cristianoag/esp32_clones/hardware/cases/apple2/preview.png

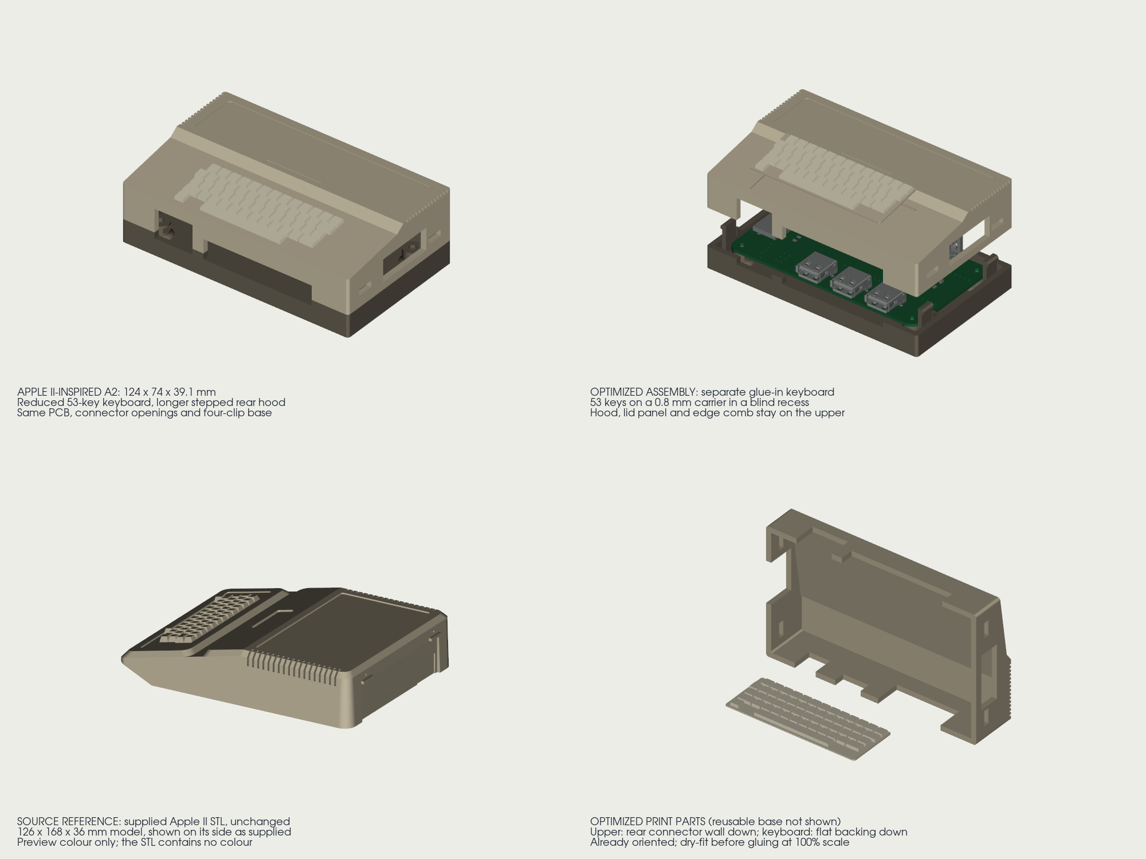
hardware/cases/apple2/preview.png
