cristianoag/esp32_clones/hardware/cases/hb-8000/preview.png

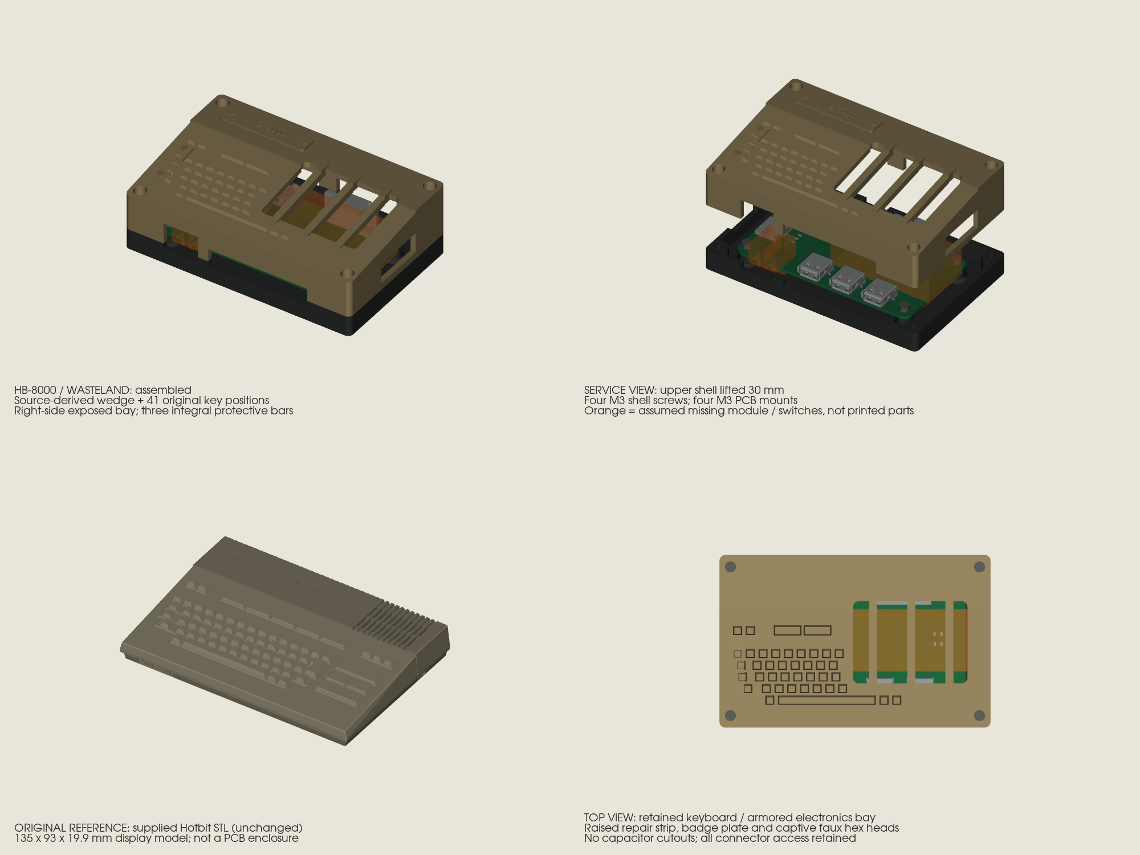
hardware/cases/hb-8000/preview.png
