cristianoag/esp32_clones/images/board-back.png

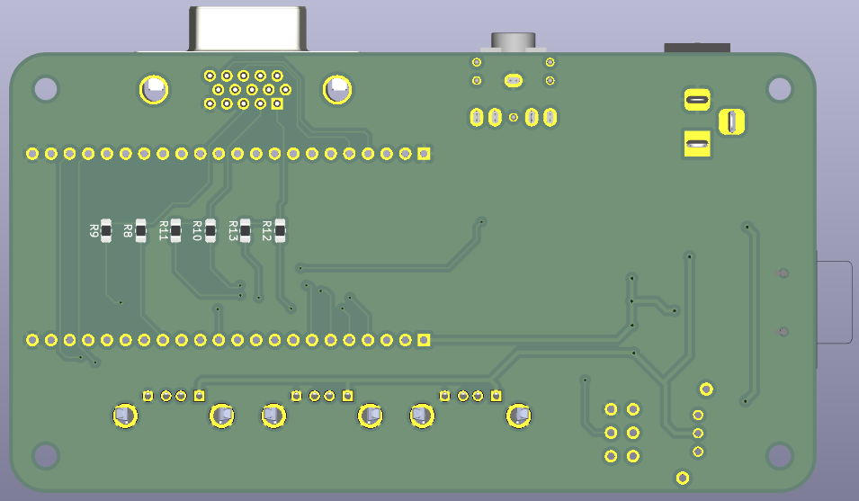
images/board-back.png
