cristianoag/esp32_clones/images/board-front.png

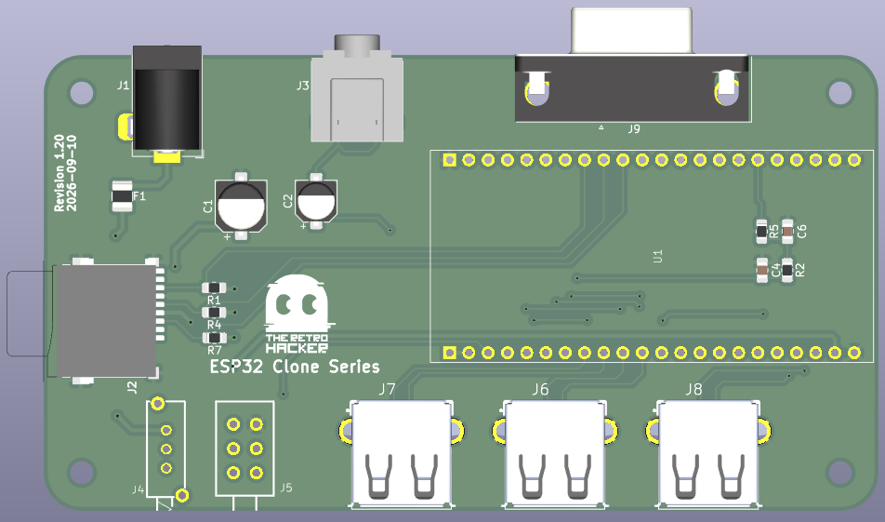
images/board-front.png
