cristianoag/esp32_clones/images/prologica.png

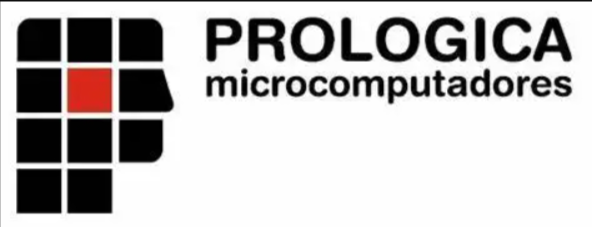
images/prologica.png
