cristianoag/esp32_clones/hardware/cases/caps/PS-12E05_cap.stl

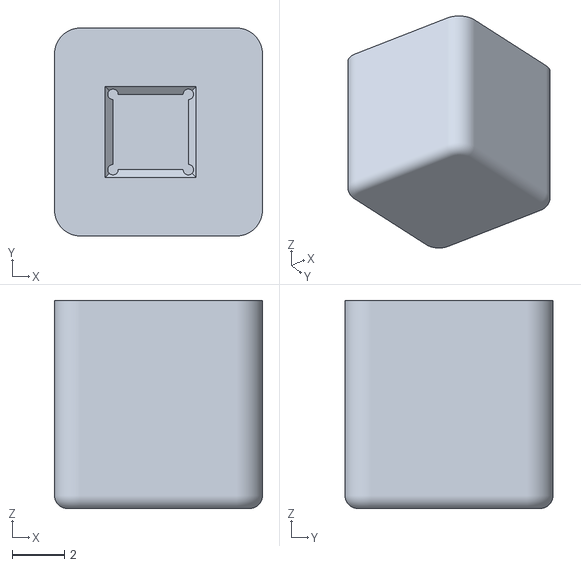
[picture p27: CAD file, 2026-10-05]
hardware/cases/caps/PS-12E05_cap.stl
8.00 x 8.00 x 8.00
