cristianoag/esp32_clones/hardware/cases/sony/f1xd_keyboard_optimized.stl

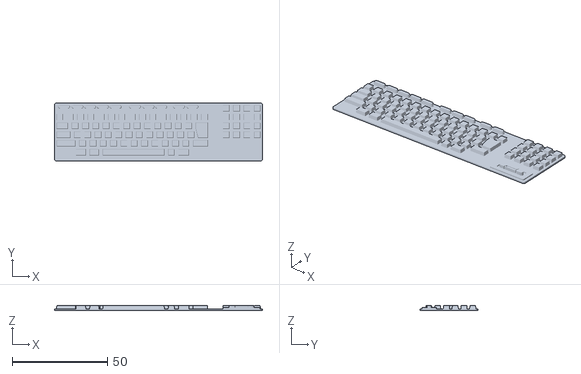
[picture p28: CAD file, 2026-10-08]
hardware/cases/sony/f1xd_keyboard_optimized.stl
109.3 x 30.4 x 2.45
