cristianoag/esp32_clones/hardware/cases/standard/upper_shell_vented.stl

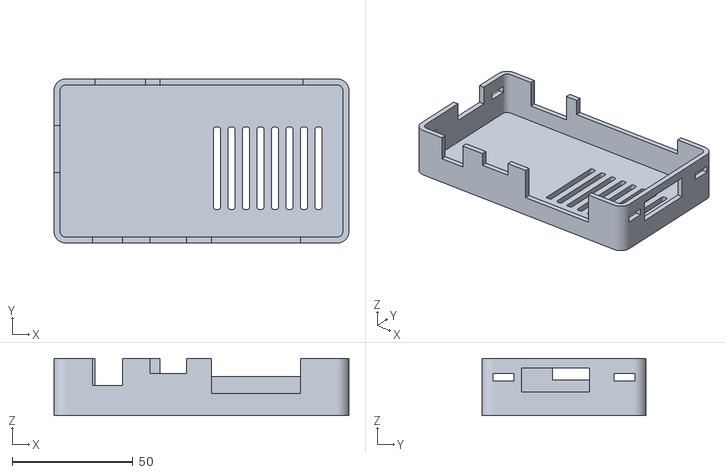
[picture p29: CAD file, 2026-10-03]
hardware/cases/standard/upper_shell_vented.stl
122.0 x 68.0 x 23.7
