cristianoag/esp32_clones/hardware/cases/apple2/apple2_base.stl

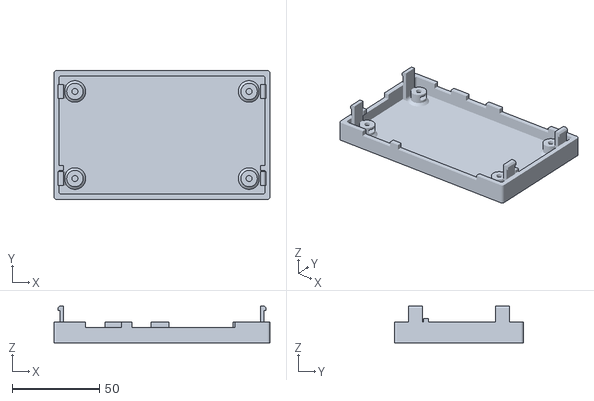
[picture p30: CAD file, 2026-10-06]
hardware/cases/apple2/apple2_base.stl
124.0 x 74.0 x 21.2
