cristianoag/esp32_clones/hardware/cases/hb-8000/wasteland_upper.stl

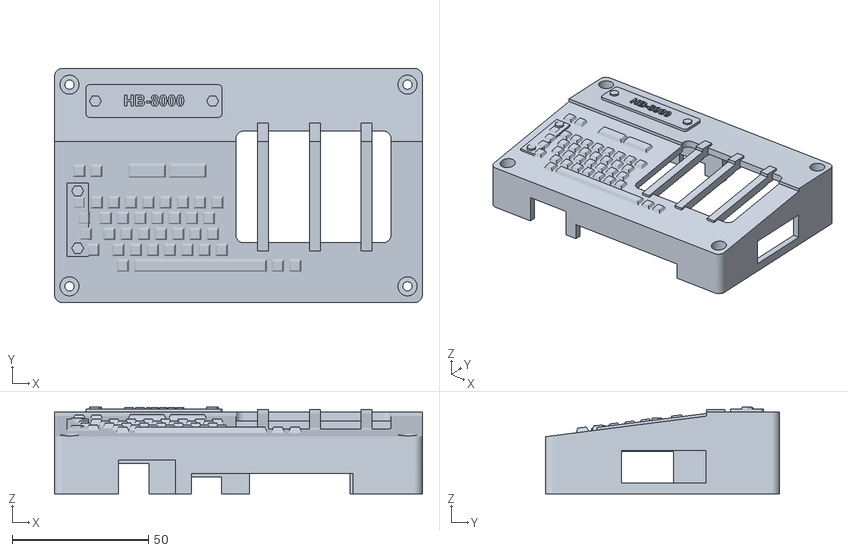
[picture p31: CAD file, 2026-10-03]
hardware/cases/hb-8000/wasteland_upper.stl
135.0 x 86.0 x 31.9
