cristianoag/esp32_clones/hardware/cases/sony/f1xd_drive_red.stl

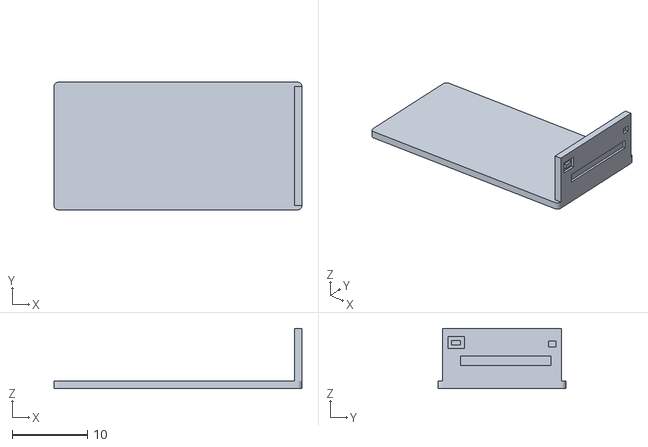
[picture p32: CAD file, 2026-10-08]
hardware/cases/sony/f1xd_drive_red.stl
33.0 x 17.0 x 8.00
