cristianoag/esp32_clones/hardware/cases/standard/lid.stl

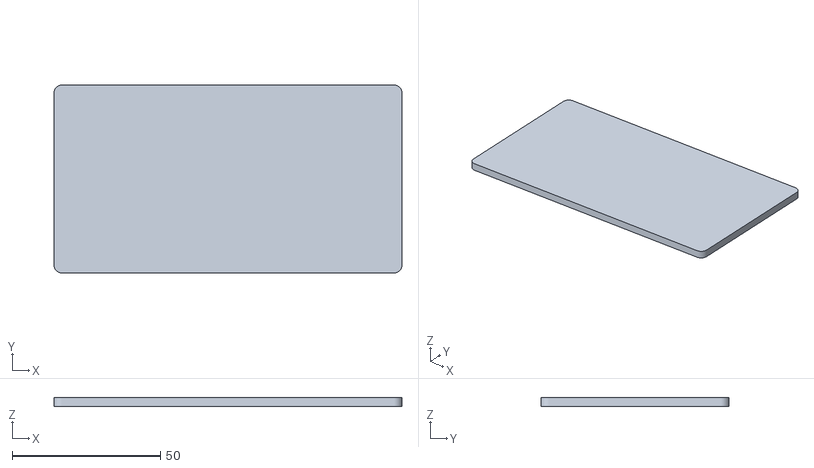
[picture p33: CAD file, 2026-10-03]
hardware/cases/standard/lid.stl
117.4 x 63.4 x 3.00
