cristianoag/esp32_clones/hardware/cases/apple2/APPLE2_1_3_scale.stl

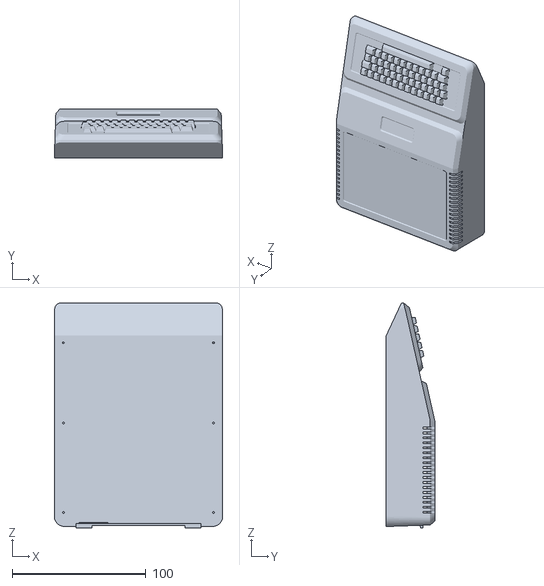
[picture p34: CAD file, 2026-10-03]
hardware/cases/apple2/APPLE2_1_3_scale.stl
126.1 x 36.3 x 168.4
