cristianoag/esp32_clones/hardware/cases/hb-8000/HB-8000_1_3_scale_open.stl

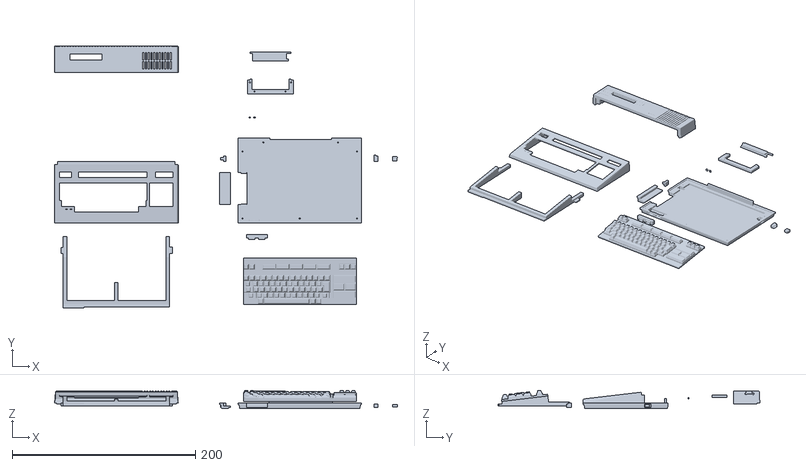
[picture p35: CAD file, 2026-10-03]
hardware/cases/hb-8000/HB-8000_1_3_scale_open.stl
374.1 x 285.5 x 19.9
