cristianoag/esp32_clones/hardware/cases/panasonic/a1st_keyboard_optimized.stl

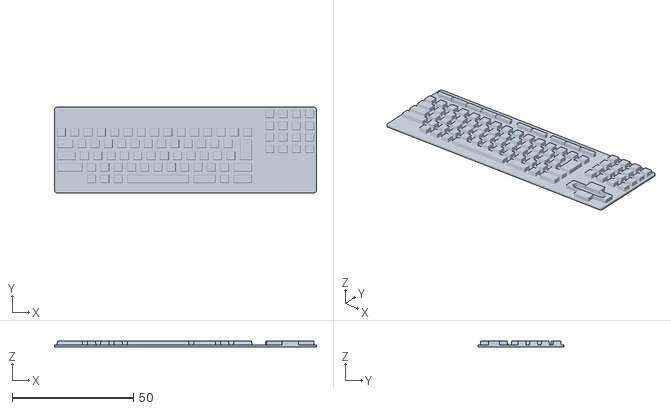
[picture p36: CAD file, 2026-10-08]
hardware/cases/panasonic/a1st_keyboard_optimized.stl
108.0 x 35.3 x 2.45
