cristianoag/esp32_clones/hardware/cases/sony/HB-F1XD_1_3_scale.stl

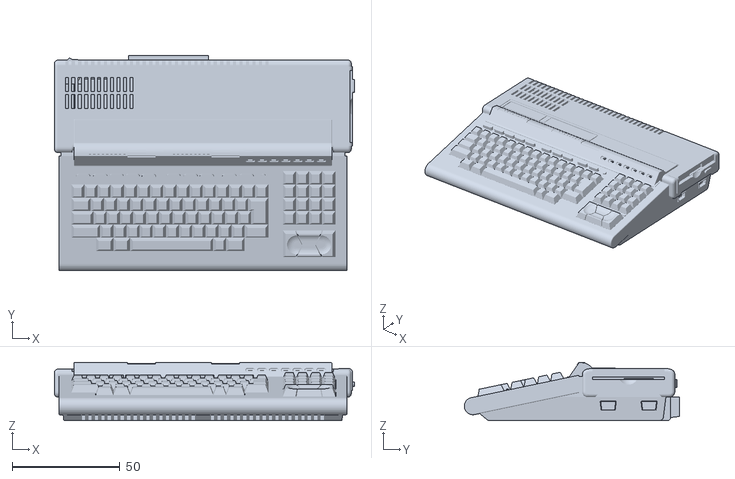
[picture p37: CAD file, 2026-10-08]
hardware/cases/sony/HB-F1XD_1_3_scale.stl
139.5 x 100.2 x 27.2
