cristianoag/esp32_clones/hardware/cases/apple2/APPLE2_1_3_scale_open.stl

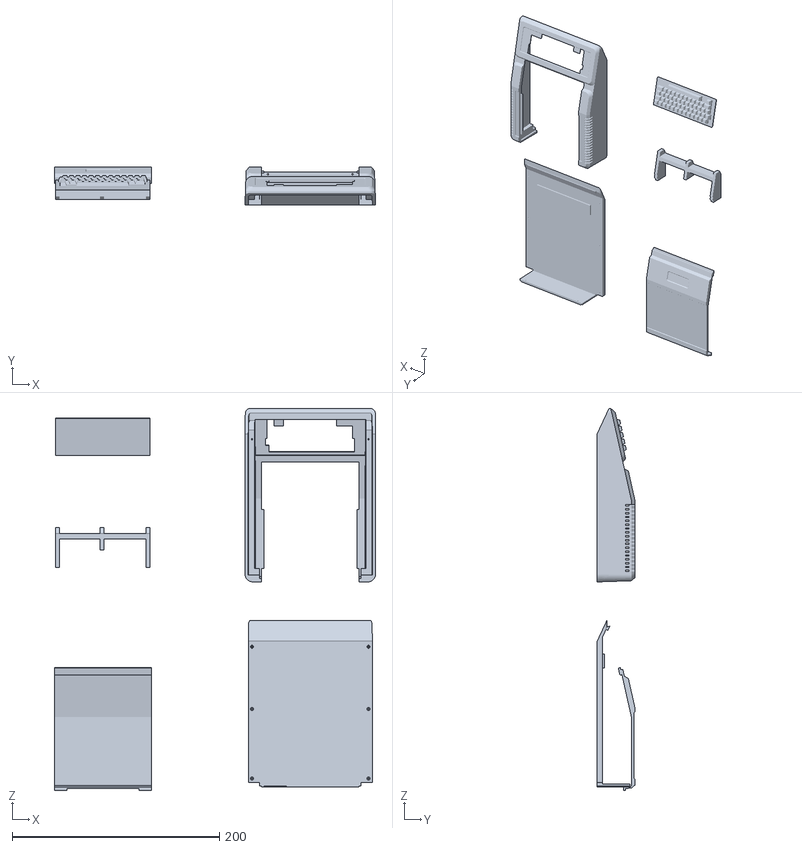
[picture p38: CAD file, 2026-10-03]
hardware/cases/apple2/APPLE2_1_3_scale_open.stl
309.9 x 36.3 x 368.4
