cristianoag/esp32_clones/hardware/cases/hb-8000/wasteland_base.stl

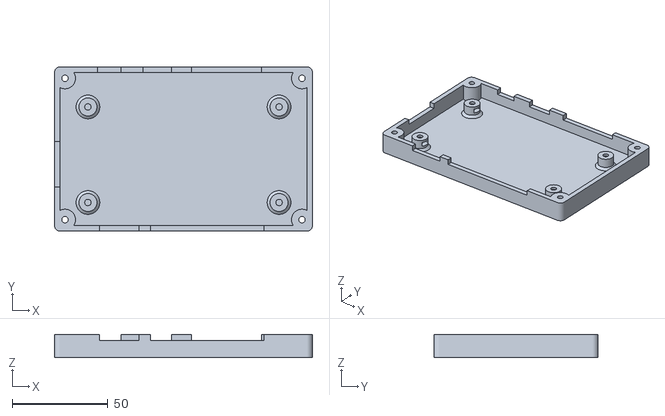
[picture p39: CAD file, 2026-10-03]
hardware/cases/hb-8000/wasteland_base.stl
135.0 x 86.0 x 12.1
