cristianoag/esp32_clones/hardware/cases/sony/HB-F1XD_1_3_scale_open.stl

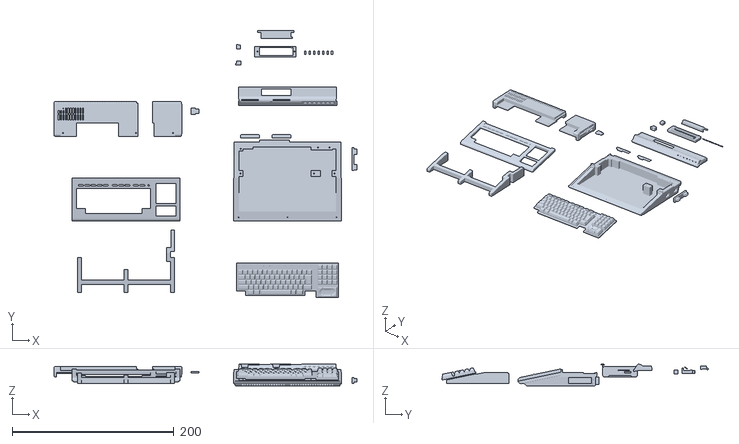
[picture p40: CAD file, 2026-10-08]
hardware/cases/sony/HB-F1XD_1_3_scale_open.stl
374.9 x 330.0 x 27.2
