cristianoag/esp32_clones/hardware/cases/apple2/APPLE2_1_3_scale_open2.stl

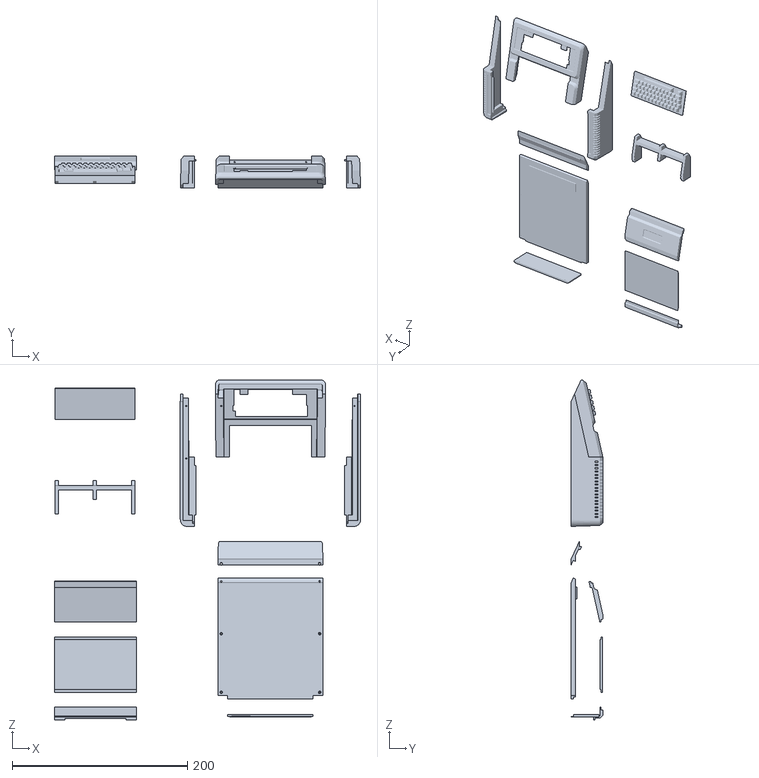
[picture p41: CAD file, 2026-10-03]
hardware/cases/apple2/APPLE2_1_3_scale_open2.stl
349.9 x 36.3 x 388.4
