cristianoag/esp32_clones/hardware/cases/hb-8000/HB-8000_1_3_scale.stl

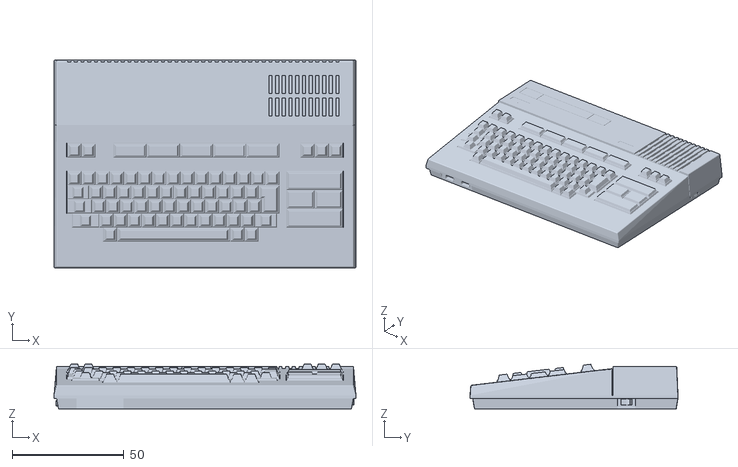
[picture p42: CAD file, 2026-10-03]
hardware/cases/hb-8000/HB-8000_1_3_scale.stl
135.0 x 93.0 x 19.9
