cristianoag/esp32_clones/software/esp32_cp400_emulator/src/CP400Roms.h

/******************************************************************************
 * Project      : esp32_cp400_emulator
 * File         : CP400Roms.h
 * Last Updated : 2026-08-17
 *
 * Description  : Font images used to emulate the CP400 video output
 *
 * Original work copyright (c) 2026 Cedric Beaudoin
 * CP400 code and modifications copyright (c) 2026 The Retro Hacker
 *
 * Permission is granted for personal, non-commercial use only.
 * Commercial use, distribution, sublicensing, or modification
 * for commercial purposes is strictly prohibited without
 * prior written permission from the author.
 * Please, keep this in the source code.
 * All rights reserved.
 ******************************************************************************/

#ifndef CP400_ROMS_H
#define CP400_ROMS_H

#include <stdint.h>


const uint8_t font_gimeChip[1536] = {
	0x00, 0x38, 0x44, 0x40, 0x40, 0x40, 0x44, 0x38, 0x10, 0x00, 0x00, 0x00,
	0x00, 0x44, 0x00, 0x44, 0x44, 0x44, 0x4c, 0x34, 0x00, 0x00, 0x00, 0x00,
	0x00, 0x08, 0x10, 0x38, 0x44, 0x7c, 0x40, 0x38, 0x00, 0x00, 0x00, 0x00,
	0x00, 0x10, 0x28, 0x38, 0x04, 0x3c, 0x44, 0x3c, 0x00, 0x00, 0x00, 0x00,
	0x00, 0x28, 0x00, 0x38, 0x04, 0x3c, 0x44, 0x3c, 0x00, 0x00, 0x00, 0x00,
	0x00, 0x20, 0x10, 0x38, 0x04, 0x3c, 0x44, 0x3c, 0x00, 0x00, 0x00, 0x00,
	0x00, 0x10, 0x00, 0x38, 0x04, 0x3c, 0x44, 0x3c, 0x00, 0x00, 0x00, 0x00,
	0x00, 0x00, 0x00, 0x38, 0x44, 0x40, 0x44, 0x38, 0x10, 0x00, 0x00, 0x00,
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
	0xff, 0xff, 0xff, 0xff, 0xff, 0xff, 0x0f, 0x0f, 0x0f, 0x0f, 0x0f, 0x0f, //13
	0xff, 0xff, 0xff, 0xff, 0xff, 0xff, 0xf0, 0xf0, 0xf0, 0xf0, 0xf0, 0xf0, //14
	0xff, 0xff, 0xff, 0xff, 0xff, 0xff, 0xff, 0xff, 0xff, 0xff, 0xff, 0xff, //15

};









#endif
