cristianoag/esp32_clones/software/esp32_msx_emulator/src/MsxCore.cpp

#include "MsxCore.h"
#include "MsxPlatform.h"
#include "Esp32Port.h"
#include "FramePacer.h"
#include "WorkProfile.h"
#include "MSX.h"
#include "Sound.h"
#include "MapperDatabase.h"
#include "AudioProfiles.h"
#include <esp_heap_caps.h>
#include <stdio.h>
#include <string.h>
#include <errno.h>
#include <sys/stat.h>
#ifdef ESP_PLATFORM
#include <esp_timer.h>
#include <freertos/FreeRTOS.h>
#include <freertos/task.h>
#endif

// Common.h needs side borders for the VDP horizontal-adjust register.
#define WIDTH 272
#define HEIGHT 240
static_assert(sizeof(pixel) == 1, "fMSX requires BPP8");
static pixel* XBuf;
static unsigned int XPal[80], BPal[256], XPal0;
static uint32_t rgbPalette[256];
static char biosDirectory[256];
static unsigned audioFraction;
static bool running;
static bool allocationFailed;
#ifdef ESP_PLATFORM
static FramePacer framePacer;
static int64_t lastYield, speedStart;
static unsigned speedFrames, speedPresented;
static FmsxWorkProfile workProfile;
extern "C" {
unsigned char fmsxProfileActive=0;
void fmsxProfileBegin(unsigned section) { workProfile.begin(section,esp_timer_get_time()); }
void fmsxProfileEnd(unsigned section) { workProfile.end(section,esp_timer_get_time()); }
}
#endif
static void PutImage();
#include "Common.h"

extern "C" void* fmsxAllocate(size_t size)
{
  void* p = heap_caps_malloc(size, MALLOC_CAP_SPIRAM | MALLOC_CAP_8BIT);
  if (!p) { allocationFailed = true; errno = ENOMEM; }
  return p;
}

extern "C" void* fmsxAllocateCpu(size_t size)
{
#ifdef ESP_PLATFORM
  // Keep video/large mapper buffers in PSRAM and leave headroom for other tasks.
  constexpr size_t reserve = 64U * 1024U;
  constexpr unsigned caps = MALLOC_CAP_INTERNAL | MALLOC_CAP_8BIT;
  void* p = nullptr;
  if (size <= 64U * 1024U && heap_caps_get_free_size(caps) >= size + reserve)
    p = heap_caps_malloc(size, caps);
  if (p) {
    printf("MSX CPU memory: %u bytes in internal SRAM\n", static_cast<unsigned>(size));
    return p;
  }
  printf("MSX CPU memory: %u bytes in PSRAM (size/reserve/fragmentation fallback)\n",
         static_cast<unsigned>(size));
#endif
  return fmsxAllocate(size);
}

extern "C" FILE* fmsxOpen(const char* name, const char* mode)
{
  if (!name) { errno = EINVAL; return nullptr; }
  if (name[0] == '/') return fopen(name, mode);
  char path[512];
  const int n = snprintf(path, sizeof(path), "%s/%s", biosDirectory, name);
  if (n < 0 || n >= static_cast<int>(sizeof(path))) {
    errno = ENAMETOOLONG;
    return nullptr;
  }
  return fopen(path, mode);
}

extern "C" void fmsxMediaYield()
{
#ifdef ESP_PLATFORM
  vTaskDelay(1);
#endif
}

extern "C" void fmsxFrame()
{
#ifdef ESP_PLATFORM
  int64_t now = esp_timer_get_time();
  workProfile.finishFrame(now);
  fmsxProfileActive=0;
  const int64_t wait = framePacer.frame(now, PALVideo);
  const int64_t target = now + wait;
  while (now < target) {
    TickType_t ticks = pdMS_TO_TICKS((target - now) / 1000);
    vTaskDelay(ticks ? ticks : 1);
    now = esp_timer_get_time();
    lastYield = now;
  }
  // Yield periodically when behind, not on every frame (one tick can be costly).
  if (now - lastYield >= 50000) {
    vTaskDelay(1);
    now = esp_timer_get_time();
    lastYield = now;
  }
  UPeriod = framePacer.renderingPercent();
  if (!speedStart) {
    speedStart = now;
    speedFrames = speedPresented = 0;
  } else ++speedFrames;
  const int64_t elapsed = now - speedStart;
  if (elapsed >= 5000000) {
    printf("MSX speed: %.1f/%u emulated fps, %.1f presented fps, draw=%u%%\n",
           speedFrames * 1000000.0 / elapsed, PALVideo ? 50U : 60U,
           speedPresented * 1000000.0 / elapsed, static_cast<unsigned>(UPeriod));
    if(workProfile.samples)
    {
      const double scale=1.0/(1000.0*workProfile.samples);
      printf("MSX work: samples=%u total=%.2f cpu/other=%.2f vdp=%.2f draw=%.2f blit=%.2f sprites=%.2f audio=%.2f input=%.2f ms/frame\n",
             workProfile.samples,workProfile.total*scale,workProfile.cpuOther()*scale,
             workProfile.times[FmsxWorkVdp]*scale,workProfile.times[FmsxWorkDraw]*scale,
             workProfile.times[FmsxWorkBlit]*scale,workProfile.times[FmsxWorkSprites]*scale,
             workProfile.times[FmsxWorkAudio]*scale,workProfile.times[FmsxWorkInput]*scale);
    }
    workProfile.clearWindow();
    speedStart = now;
    speedFrames = speedPresented = 0;
  }
  now=esp_timer_get_time();
  framePacer.released(now);
  fmsxProfileActive=workProfile.startFrame(now);
#endif
  if (msxShouldExit()) ExitNow = 1;
}

static void PutImage()
{
  FMSX_WORK_BEGIN(FmsxWorkBlit);
  const int width = 256;
  msxPresent(XBuf + (WIDTH - width) / 2, width, HEIGHT, rgbPalette, WIDTH);
  FMSX_WORK_END(FmsxWorkBlit);
#ifdef ESP_PLATFORM
  ++speedPresented;
#endif
  if (msxShouldExit()) ExitNow = 1;
}

extern "C" void SetColor(byte n, byte r, byte g, byte b)
{
  if (n >= 80) return;
  // A fixed GGGRRRBB palette preserves scanline palette changes and SCREEN 8/YJK.
  XPal[n] = (g & 0xE0) | ((r & 0xE0) >> 3) | (b >> 6);
  if (!n) XPal0 = XPal[n];
}

extern "C" void Keyboard()
{
  uint8_t matrix[16];
  memset(matrix, 0xFF, sizeof(matrix));
#ifdef ESP_PLATFORM
  const int64_t pollStart = esp_timer_get_time();
#endif
  msxPollKeyboard(matrix);
#ifdef ESP_PLATFORM
  // F12 menus block inside the platform callback. Discard their wall time/debt.
  if (esp_timer_get_time() - pollStart >= 100000) {
    framePacer.reset(true);
    workProfile.reset();
    fmsxProfileActive=0;
    speedStart = 0;
    speedFrames = speedPresented = 0;
  }
#endif
  for (unsigned i = 0; i < sizeof(matrix); ++i) KeyState[i] = matrix[i];
  if (msxShouldExit()) ExitNow = 1;
}

extern "C" unsigned int Joystick() { return msxPollJoysticks() & 0x3f3f; }
extern "C" unsigned int Mouse(byte) { return 0; }
extern "C" unsigned int InitAudio(unsigned int rate, unsigned int) { return rate; }
extern "C" void TrashAudio() {}
extern "C" unsigned int GetFreeAudio() { return 1024; }
extern "C" unsigned int WriteAudio(sample* data, unsigned int count)
{
  static_assert(sizeof(sample) == sizeof(int16_t), "fMSX requires BPS16");
  msxSubmitAudio(data, count);
  return count;
}

extern "C" void PlayAllSound(int microseconds)
{
  audioFraction += static_cast<unsigned>(microseconds) * 22050U;
  const unsigned samples = audioFraction / 1000000U;
  audioFraction %= 1000000U;
  if (samples) RenderAndPlayAudio(samples);
}

bool MsxValidateCartridge(const char* path, char* error, size_t errorSize)
{
  if (error && errorSize) error[0] = 0;
  if (!path || !*path) return true;
  const char* problem = nullptr;
  struct stat info;
  if (path[0] != '/')
    problem = "requires an absolute path";
  else if (stat(path, &info) != 0 || !S_ISREG(info.st_mode))
    problem = "file is missing or is not a regular file";
  else if (info.st_size < 8192 || info.st_size > MSX_MAX_CART_BYTES ||
           (info.st_size % 8192) != 0)
    problem = "invalid ROM size (8 KiB multiples, maximum 2 MiB)";
  if (!problem) {
    FILE* file = fopen(path, "rb");
    if (!file) problem = "cannot open cartridge ROM";
    else {
      bool signature = false;
      const long offsets[] = {0, 0x4000, static_cast<long>(info.st_size) - 0x4000};
      for (long offset : offsets) {
        if (offset < 0 || offset + 2 > info.st_size) continue;
        unsigned char header[2];
        if (fseek(file, offset, SEEK_SET) != 0 ||
            fread(header, 1, sizeof(header), file) != sizeof(header)) {
          problem = "cannot read cartridge ROM header";
          break;
        }
#ifdef ESP_PLATFORM
        vTaskDelay(1);
#endif
        if (header[0] == 'A' && header[1] == 'B') { signature = true; break; }
      }
      if (!problem && !signature) problem = "invalid cartridge ROM (AB header not found)";
      fclose(file);
    }
  }
  if (problem && error && errorSize) snprintf(error, errorSize, "%s", problem);
  return !problem;
}

static bool validateCartridge(const char* path, int slot)
{
  char error[128];
  if (MsxValidateCartridge(path, error, sizeof(error))) return true;
  char message[192];
  snprintf(message, sizeof(message), "MSX slot %d: %s.", slot, error);
  msxReportError(message);
  return false;
}

static bool mediaResult(const char* problem, char* error, size_t size)
{
  if (error && size) snprintf(error, size, "%s", problem ? problem : "");
  return !problem;
}

bool MsxInspectCartridge(const char* path, const char* profileDirectory,
                         MsxCartridgeInfo& info, char* error, size_t errorSize)
{
  if (!path || !*path || !profileDirectory || profileDirectory[0] != '/' ||
      strlen(profileDirectory) >= sizeof(biosDirectory))
    return mediaResult("inspection requires cartridge and absolute BIOS directory", error, errorSize);
  if (!MsxValidateCartridge(path, error, errorSize)) return false;
  struct stat fileInfo;
  if (stat(path, &fileInfo) || fileInfo.st_size < 8192 ||
      fileInfo.st_size > MSX_MAX_CART_BYTES || fileInfo.st_size % 8192)
    return mediaResult("cartridge size changed during inspection", error, errorSize);
  FILE* file = fopen(path, "rb");
  if (!file) return mediaResult("cannot open cartridge for inspection", error, errorSize);
  const size_t size = static_cast<size_t>(fileInfo.st_size);
  auto* data = static_cast<unsigned char*>(heap_caps_malloc(size, MALLOC_CAP_SPIRAM | MALLOC_CAP_8BIT));
  if (!data) {
    fclose(file);
    return mediaResult("not enough PSRAM to inspect cartridge; previous selection retained", error, errorSize);
  }
  const char* problem = nullptr;
  for (size_t offset = 0; offset < size;) {
    const size_t count = size - offset < 16384 ? size - offset : 16384;
    if (fread(data + offset, 1, count, file) != count) { problem = "cannot fully read cartridge"; break; }
    offset += count;
#ifdef ESP_PLATFORM
    vTaskDelay(1);
#endif
  }
  if (!problem && (fgetc(file) != EOF || ferror(file))) problem = "cartridge changed during inspection";
  fclose(file);
  FILE* databases[2] = {};
  MsxCartridgeInfo detected = {-1, "ROM layout"};
  if (!problem) {
    const bool ab0 = data[0] == 'A' && data[1] == 'B';
    const bool ab4000 = size > 0x4001 && data[0x4000] == 'A' && data[0x4001] == 'B';
    const bool abLast = size >= 16384 && data[size - 16384] == 'A' && data[size - 16383] == 'B';
    if (!ab0 && !ab4000 && !abLast) problem = "cartridge header changed during inspection";
    else if (size > 32768 && !(!ab0 && ab4000)) {
      const char* names[] = {"CARTS.CRC", "CARTS.SHA"};
      for (unsigned i = 0; i < 2; ++i) {
        char databasePath[512];
        snprintf(databasePath, sizeof(databasePath), "%s/%s", profileDirectory, names[i]);
        errno = 0;
        databases[i] = fopen(databasePath, "rb");
        if (!databases[i] && errno != ENOENT) { problem = "cannot read mapper override database"; break; }
      }
      if (!problem) {
        detected.detectedMapper = GuessROMWithFiles(data, size, databases[0], databases[1], &detected.source);
        if (detected.detectedMapper <= -100) problem = FmsxUnsupportedMapperName(detected.detectedMapper);
      }
    }
  }
  for (FILE* database : databases) if (database) fclose(database);
  heap_caps_free(data);
  if (!problem) info = detected;
  return mediaResult(problem, error, errorSize);
}

static bool validateMedia(const char* path, bool tape, char* error, size_t size)
{
  if (!path || !*path) return mediaResult(nullptr, error, size);
  struct stat info;
  if (path[0] != '/')
    return mediaResult("requires an absolute path", error, size);
  if (stat(path, &info) || !S_ISREG(info.st_mode))
    return mediaResult("file is missing or is not a regular file", error, size);
  if (!tape && info.st_size != 368640 && info.st_size != 737280)
    return mediaResult("DSK must be raw 360 or 720 KiB", error, size);
  FILE* file = fopen(path, tape ? "rb" : "r+b");
  if (!file) return mediaResult(tape ? "cannot open tape read-only" :
                               "disk is not writable; check file/SD write protection", error, size);
  const unsigned char marker[] = {0x1F,0xA6,0xDE,0xBA,0xCC,0x13,0x7D,0x74};
  unsigned char header[8];
  const size_t count = fread(header, 1, sizeof(header), file);
  fclose(file);
  if (count != sizeof(header))
    return mediaResult("cannot read media header", error, size);
  if (tape && memcmp(header, marker, sizeof(marker)))
    return mediaResult("invalid CAS marker (WAV is not supported)", error, size);
  return mediaResult(nullptr, error, size);
}

bool MsxValidateDisk(const char* path, char* error, size_t size)
{
  return validateMedia(path, false, error, size);
}

bool MsxValidateTape(const char* path, char* error, size_t size)
{
  return validateMedia(path, true, error, size);
}

bool MsxDiskAvailable() { return running && DiskROMAvailable(); }

bool MsxAttachDisk(unsigned drive, const char* path, char* error, size_t size)
{
  if (drive >= 2) return mediaResult("only disk drives A and B are available", error, size);
  if (!running) return mediaResult("MSX is not running", error, size);
  if (!MsxValidateDisk(path, error, size)) return false;
  if (path && *path && !MsxDiskAvailable())
    return mediaResult("add compatible DISK.ROM to this BIOS profile and cold boot", error, size);
  if (!ChangeDisk(drive, path))
    return mediaResult(errno == ENOMEM ? "not enough PSRAM for disk; previous disk retained" :
                       errno == EBUSY ? "disk already attached to another drive; eject it there first" :
                       DiskLoadLastError(), error, size);
  return mediaResult(nullptr, error, size);
}

bool MsxAttachTape(const char* path, char* error, size_t size)
{
  if (!running) return mediaResult("MSX is not running", error, size);
  if (!MsxValidateTape(path, error, size)) return false;
  if (!ChangeTape(path))
    return mediaResult("cannot read CAS; previous tape retained", error, size);
  return mediaResult(nullptr, error, size);
}

bool MsxRewindTape(char* error, size_t size)
{
  if (!running || !CasStream) return mediaResult("no tape attached", error, size);
  clearerr(CasStream);
  if (fseek(CasStream, 0, SEEK_SET))
    return mediaResult("cannot rewind tape; check SD card", error, size);
  return mediaResult(nullptr, error, size);
}

bool MsxCoreRun(const char* romDirectory, int model, int ramPages,
                const char* slot1, const char* slot2,
                const char* diskA, const char* diskB, const char* tape,
                unsigned mapper1, unsigned mapper2, unsigned audioProfile)
{
  static_assert(MsxGeneric8 == MAP_GEN8 && MsxGeneric16 == MAP_GEN16 &&
                MsxKonamiScc == MAP_KONAMI5 && MsxKonami == MAP_KONAMI4 &&
                MsxAscii8 == MAP_ASCII8 && MsxAscii16 == MAP_ASCII16 &&
                MsxGameMaster2 == MAP_GMASTER2 && MsxFmPac == MAP_FMPAC, "Mapper IDs must match fMSX.");
  if (!MsxValidMapper(mapper1) || !MsxValidMapper(mapper2)) {
    msxReportError("Invalid cartridge mapper override.");
    return false;
  }
  if (!MsxAudioProfileValid(audioProfile)) {
    msxReportError("Invalid audio profile.");
    return false;
  }
  if (running || !romDirectory || romDirectory[0] != '/' ||
      strlen(romDirectory) >= sizeof(biosDirectory) || model < 0 || model > 2 ||
      (ramPages != 4 && ramPages != 8 && ramPages != 16 && ramPages != 32)) {
    msxReportError("Invalid MSX model, RAM size, BIOS directory, or concurrent run.");
    return false;
  }
  if (!validateCartridge(slot1, 1) || !validateCartridge(slot2, 2)) return false;
  char mediaError[160];
  if (!MsxValidateDisk(diskA, mediaError, sizeof(mediaError)) ||
      !MsxValidateDisk(diskB, mediaError, sizeof(mediaError)) ||
      !MsxValidateTape(tape, mediaError, sizeof(mediaError))) {
    msxReportError(mediaError);
    return false;
  }
  char fmRomPath[512];
  if (!MsxResolveAudioProfile(audioProfile, romDirectory, fmRomPath, sizeof(fmRomPath),
                             mediaError, sizeof(mediaError))) {
    msxReportError(mediaError);
    return false;
  }
  if (!FmsxSetAudioProfile(audioProfile, fmRomPath[0] ? fmRomPath : nullptr)) {
    msxReportError("Cannot configure MSX audio profile.");
    return false;
  }
  running = true;
  allocationFailed = false;
  strcpy(biosDirectory, romDirectory);
  XBuf = static_cast<pixel*>(fmsxAllocate(WIDTH * HEIGHT * sizeof(pixel)));
  if (!XBuf) {
    heap_caps_free(XBuf);
    XBuf = nullptr;
    running = false;
    FmsxSetAudioProfile(MsxAudioAuto, nullptr);
    msxReportError("Not enough PSRAM for MSX video.");
    return false;
  }
  memset(XBuf, 0, WIDTH * HEIGHT * sizeof(pixel));
  memset(XPal, 0, sizeof(XPal));
  XPal0 = 0;
  for (unsigned i = 0; i < 256; ++i) {
    BPal[i] = i;
    rgbPalette[i] = (((i >> 2) & 7) * 255 / 7 << 16) |
                    (((i >> 5) & 7) * 255 / 7 << 8) | ((i & 3) * 255 / 3);
  }
  audioFraction = 0;
#ifdef ESP_PLATFORM
  framePacer.reset();
  workProfile.reset();
  fmsxProfileActive=0;
  lastYield = esp_timer_get_time();
  speedStart = 0;
  speedFrames = speedPresented = 0;
#endif
  InitSound(22050, 0);
  SetNoise(0x10000, 16, 14);
  SetChannels(128, (1 << MAXCHANNELS) - 1);
  // Use explicit profile-root resolution rather than fMSX's desktop chdir model.
  ProgDir = nullptr;
  Verbose = 0;
  UPeriod = 100;
  for (int i = 0; i < MAXCARTS; ++i) ROMName[i] = nullptr;
  ROMName[0] = slot1 && *slot1 ? slot1 : nullptr;
  ROMName[1] = slot2 && *slot2 ? slot2 : nullptr;
  for (int i = 0; i < MAXDRIVES; ++i) DSKName[i] = nullptr;
  DSKName[0] = diskA && *diskA ? diskA : nullptr;
  DSKName[1] = diskB && *diskB ? diskB : nullptr;
  SndName = PrnName = CasName = ComName = STAName = FNTName = nullptr;
  CasName = tape && *tape ? tape : nullptr;
  CPU.Trap = 0xFFFF;
  CPU.Trace = 0;
  printf("MSX audio: %s%s%s\n", MsxAudioProfileName(audioProfile),
         fmRomPath[0] ? "; BIOS: " : "", fmRomPath);
  errno = 0;
  const int mapperMode = (mapper1 == MsxMapperAuto ? MSX_GUESSA : mapper1 << 8) |
                        (mapper2 == MsxMapperAuto ? MSX_GUESSB : mapper2 << 12);
  const bool result = StartMSX(model | MSX_NTSC | mapperMode | MSX_PATCHBDOS |
                               (JOY_STICK << 4) | (JOY_STICK << 6),
                               ramPages, model ? 8 : 2) != 0;
  const int bootError = errno;
  char diskLoadError[160];
  snprintf(diskLoadError, sizeof(diskLoadError), "%s", DiskLoadLastError());
  ResetVDP();
  TrashMSX();
#ifdef ESP_PLATFORM
  fmsxProfileActive=0;
#endif
  FmsxSetAudioProfile(MsxAudioAuto, nullptr);
  for (int i = 0; i < MAXCARTS; ++i) ROMName[i] = nullptr;
  for (int i = 0; i < MAXDRIVES; ++i) DSKName[i] = nullptr;
  CasName = nullptr;
  TrashSound();
  heap_caps_free(XBuf);
  XBuf = nullptr;
  running = false;
  if (!result) {
    if (allocationFailed || bootError == ENOMEM)
      msxReportError("Not enough PSRAM to load the MSX BIOS, RAM, cartridges or disks.");
    else if (bootError == ENODEV)
      msxReportError("Add compatible DISK.ROM to this BIOS profile and cold boot to attach disks.");
    else if (bootError == EBUSY)
      msxReportError("The same disk cannot be attached to A and B. Select separate writable images.");
    else if (bootError == ENOTSUP)
      msxReportError("Cartridge mapper is not emulated. See UART for the detected mapper.");
    else if (bootError == ENOEXEC || bootError == EFBIG)
      msxReportError("Invalid cartridge ROM: check the AB header and size (maximum 2 MiB).");
    else if (diskLoadError[0])
      msxReportError(diskLoadError);
    else
      msxReportError("MSX boot failed: check BIOS, cartridges and writable disk images on SD.");
  }
  return result;
}
