cristianoag/esp32_clones/software/esp32_apple2_emulator/src/AppleBoard.h

#pragma once

namespace AppleBoard
{
constexpr int VSync = 1;
constexpr int HSync = 2;
constexpr int RedLow = 5;
constexpr int RedHigh = 4;
constexpr int GreenLow = 7;
constexpr int GreenHigh = 6;
constexpr int BlueLow = 9;
constexpr int BlueHigh = 8;
constexpr int SdCmd = 38;
constexpr int SdClk = 39;
constexpr int SdData = 40;
constexpr int Audio = 47;
constexpr int RgbLed = 48;
constexpr int Width = 640;
constexpr int Height = 240;
constexpr unsigned AudioRate = 22050;
}
