cristianoag/esp32_clones/software/esp32_msx_emulator/src/MsxMenuLayout.h

#pragma once
#include <stddef.h>

enum MsxMenuItem : unsigned
{
    MsxMenuResume, MsxMenuBios,  MsxMenuRam, MsxMenuMedia,
    MsxMenuSound, MsxMenuAutoBoot, MsxMenuSave, MsxMenuBoot, MsxMenuRescan,
    MsxMenuUpdate, MsxMenuJoysticks, MsxMenuCount
};

enum MsxMediaItem : unsigned
{
    MsxMediaSlot1, MsxMediaMapper1, MsxMediaSlot2, MsxMediaMapper2,
    MsxMediaDiskA, MsxMediaDiskB, MsxMediaTape, MsxMediaRewind,
    MsxMediaAudio, MsxMediaSaveBoot, MsxMediaBoot, MsxMediaCount
};

constexpr int MsxMenuTop = 48;
constexpr int MsxMenuRowHeight = 8;
constexpr size_t MsxBrowserPageSize = 16;
constexpr int MsxMenuRowY(unsigned row) { return MsxMenuTop + row * MsxMenuRowHeight; }
static_assert(MsxMenuRowY(MsxMenuCount) < 180, "Menu must not overlap navigation hints.");
static_assert(MsxMenuRowY(MsxMediaCount) <= 140, "Media must not overlap its details.");
static_assert(MsxMenuRowY(MsxBrowserPageSize) <= 180, "File list must not overlap page information.");

inline size_t MsxMoveSelection(size_t current, int direction, size_t count)
{
    if (!count) return 0;
    return direction < 0 ? (current ? current - 1 : count - 1) : (current + 1) % count;
}
