cristianoag/esp32_clones/software/esp32_apple2_emulator/tests/JoystickMappingTests.cpp

#include "AppleJoystickMapping.h"

#include <assert.h>
#include <initializer_list>
#include <stdio.h>
#include <string.h>
#include <type_traits>

namespace {
const uint8_t directions[9] = {0, 1, 9, 8, 10, 2, 6, 4, 5};
typedef AppleJoystickSample Samples[11];

AppleJoystickMapping build(uint8_t length, const Samples &samples)
{
    AppleJoystickMapping result = {};
    char error[128] = {};
    if (!AppleBuildJoystickMapping(length, samples, result, error, sizeof(error))) {
        fprintf(stderr, "Calibration failed: %s\n", error);
        assert(false);
    }
    assert(!error[0]);
    assert(AppleValidJoystickMapping(result));
    return result;
}

void check(const AppleJoystickMapping &m, const uint8_t *report, uint8_t expected)
{
    uint8_t result = 255;
    const bool decoded = AppleDecodeJoystickReport(m, report, m.length, result);
    if (!decoded || result != expected) {
        fprintf(stderr, "Decode expected %02x, got %02x (%s), report:", expected, result, decoded ? "valid" : "invalid");
        for (unsigned i = 0; i < m.length; ++i) fprintf(stderr, " %02x", report[i]);
        fprintf(stderr, "\n");
    }
    assert(decoded);
    assert(result == expected);
}

void reject(const AppleJoystickMapping &m, const uint8_t *report, size_t length)
{
    uint8_t result = 255;
    assert(!AppleDecodeJoystickReport(m, report, length, result));
    assert(result == 0);
}

void rejectedBuild(uint8_t length, const Samples &samples)
{
    AppleJoystickMapping result;
    memset(&result, 0xff, sizeof(result));
    char error[128] = {};
    assert(!AppleBuildJoystickMapping(length, samples, result, error, sizeof(error)));
    assert(error[0]);
    assert(!AppleValidJoystickMapping(result));
    const AppleJoystickMapping empty = {};
    assert(!memcmp(&result, &empty, sizeof(result)));
}

void testPackedDpad()
{
    Samples samples = {};
    for (unsigned p = 0; p < 9; ++p) samples[p].bytes[0] = directions[p];
    samples[9].bytes[0] = 0x10;
    samples[10].bytes[0] = 0x20;
    const AppleJoystickMapping m = build(1, samples);
    for (unsigned p = 0; p < 9; ++p) {
        for (unsigned b = 0; b < 4; ++b) {
            const uint8_t report = directions[p] | (b << 4);
            check(m, &report, report);
        }
    }
    for (uint8_t contradiction : {uint8_t(3), uint8_t(12), uint8_t(15)})
        reject(m, &contradiction, 1);
    uint8_t extraUnusedButton = 0xc1;
    check(m, &extraUnusedButton, 1);
}

void testPackedHatAndActiveLowButtons()
{
    Samples samples = {};
    // Nonstandard but distinct clockwise hat encoding.
    const uint8_t hat[9] = {15, 7, 2, 5, 0, 6, 3, 1, 4};
    for (unsigned p = 0; p < 11; ++p) {
        samples[p].bytes[0] = 9; // Report ID.
        samples[p].bytes[1] = 0x30 | hat[p < 9 ? p : 0];
        samples[p].bytes[2] = uint8_t(p * 17);
        samples[p].changed[2] = 0xff; // Free-running counter.
    }
    samples[9].bytes[1] &= ~0x10;
    samples[10].bytes[1] &= ~0x20;
    const AppleJoystickMapping m = build(3, samples);
    assert(m.fixedMask[0] == 0xff);
    assert(m.ignored[2] == 0xff);
    for (unsigned p = 0; p < 9; ++p) {
        for (unsigned b = 0; b < 4; ++b) {
            uint8_t report[3] = {9, uint8_t(hat[p] | (0x30 ^ (b << 4))), 241};
            check(m, report, directions[p] | (b << 4));
        }
    }
    uint8_t report[4] = {9, 0x3e, 0, 0};
    reject(m, report, 3); // Unknown hat code.
    report[1] = 0x3f;
    report[0] = 8;
    reject(m, report, 3); // Wrong report ID.
    report[0] = 9;
    reject(m, report, 2);
    reject(m, report, 4);
    reject(m, 0, 3);
}

Samples &axisSamples(Samples &samples, bool signedAxes, bool reversed)
{
    memset(samples, 0, sizeof(samples));
    for (unsigned p = 0; p < 11; ++p) {
        const uint8_t bits = p < 9 ? directions[p] : 0;
        samples[p].bytes[0] = 4;
        for (unsigned a = 0; a < 2; ++a) {
            const uint8_t negative = a ? 1 : 4, positive = a ? 2 : 8;
            const bool diagonal = (bits & 3) && (bits & 12);
            int offset = (bits & negative) ? -(diagonal ? 80 : 120) :
                         (bits & positive) ? (diagonal ? 80 : 120) : 0;
            if (reversed) offset = -offset;
            samples[p].bytes[1 + a] = uint8_t(offset + (signedAxes ? 0 : 128));
        }
        samples[p].bytes[3] = p == 9 ? 0x40 : p == 10 ? 2 : 0;
        samples[p].bytes[4] = uint8_t(p * 23);
        samples[p].changed[4] = 0xff;
    }
    return samples;
}

void testAxes()
{
    for (unsigned signedAxes = 0; signedAxes < 2; ++signedAxes) {
        for (unsigned reversed = 0; reversed < 2; ++reversed) {
            Samples samples;
            axisSamples(samples, signedAxes != 0, reversed != 0);
            const AppleJoystickMapping m = build(5, samples);
            assert(m.axes[0].byteIndex == 1);
            assert(m.axes[1].byteIndex == 2);
            assert(m.axes[0].signFlip == (signedAxes ? 0x80 : 0));
            for (unsigned p = 0; p < 11; ++p)
                check(m, samples[p].bytes, p < 9 ? directions[p] : uint8_t(0x10 << (p - 9)));
            const int center = signedAxes ? 0 : 128;
            uint8_t report[5] = {4, uint8_t(center + 10), uint8_t(center - 10), 0, 255};
            check(m, report, 0); // Neutral deadzone.
            report[1] = uint8_t(center + (reversed ? 70 : -70));
            report[2] = uint8_t(center + (reversed ? -70 : 70));
            report[3] = 0x42;
            check(m, report, 6 | 0x30); // Intermediate down-left with both buttons.
            report[1] = report[2] = uint8_t(center);
            check(m, report, 0x30);
        }
    }
}
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
